YeetTheAnson/AnsonKeyboardNew/assets/render6.png

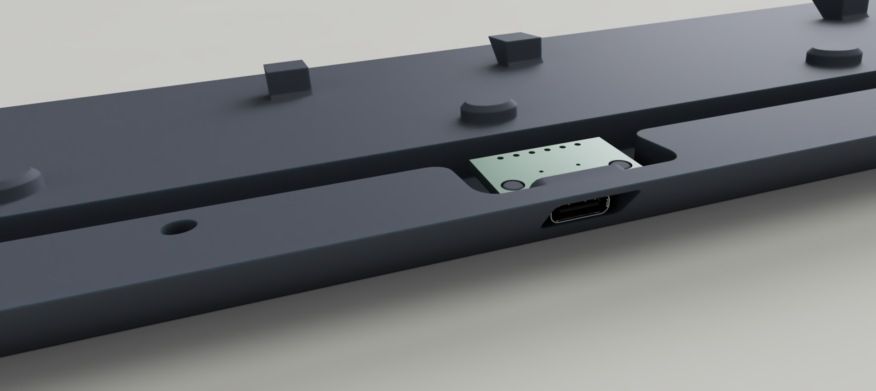
assets/render6.png
