YeetTheAnson/AnsonKeyboardNew/PCB/3d/keycap/DSA_6.25u.step

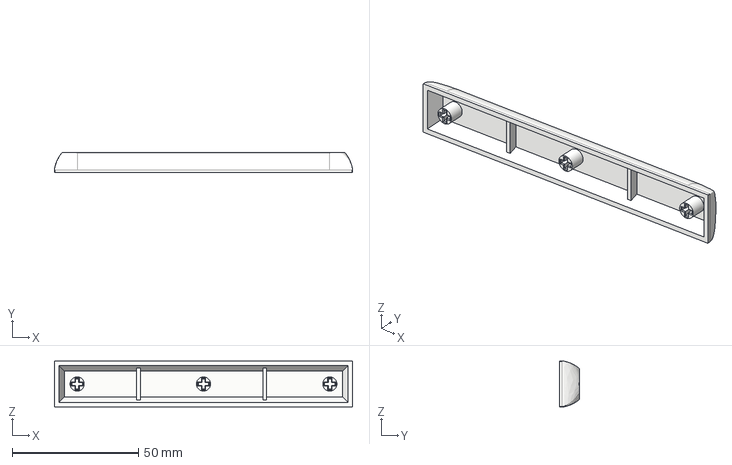
[picture p33: CAD file, 2025-10-06]
PCB/3d/keycap/DSA_6.25u.step
118.0 x 8.00 x 18.2 mm
