YeetTheAnson/AnsonKeyboardNew/PCB/3d/RASPBERRY_PI_PICO.step

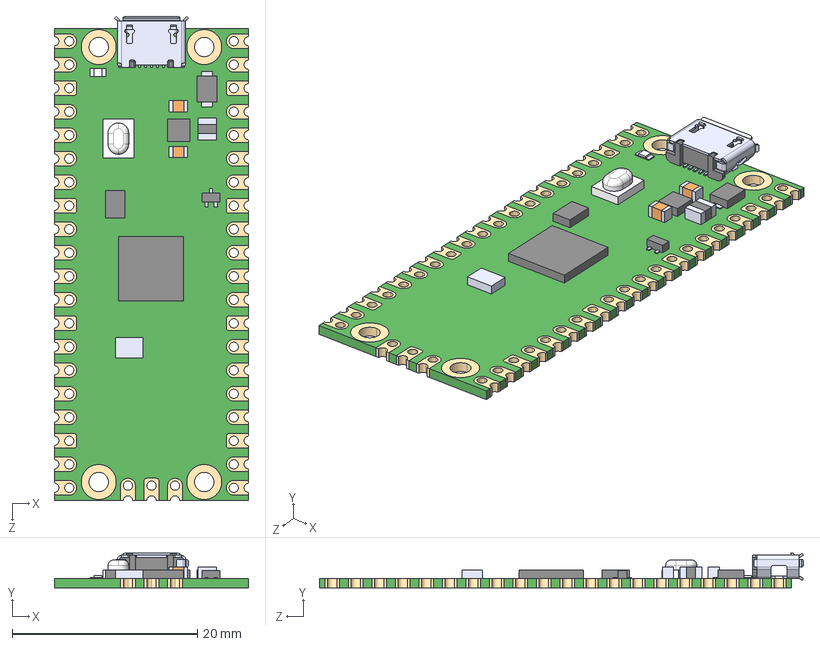
[picture p34: CAD file, 2025-10-06]
PCB/3d/RASPBERRY_PI_PICO.step
21.0 x 3.73 x 52.3 mm
