YeetTheAnson/AnsonKeyboardNew/PCB/3d/keycap/DSA_2u.step

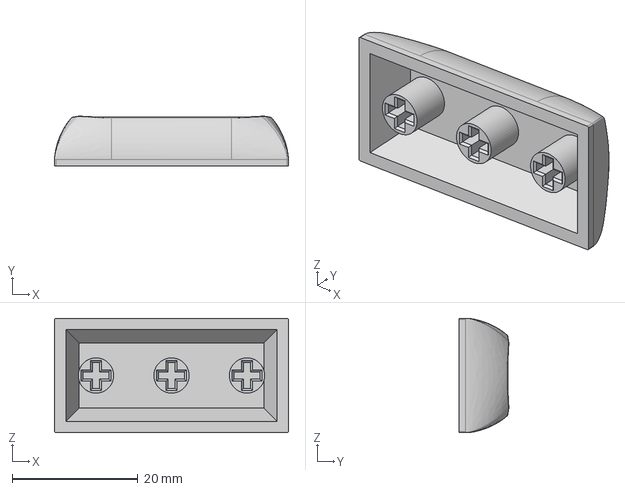
[picture p35: CAD file, 2025-10-06]
PCB/3d/keycap/DSA_2u.step
37.2 x 7.91 x 18.2 mm
