YeetTheAnson/AnsonKeyboardNew/PCB/3d/switch.step

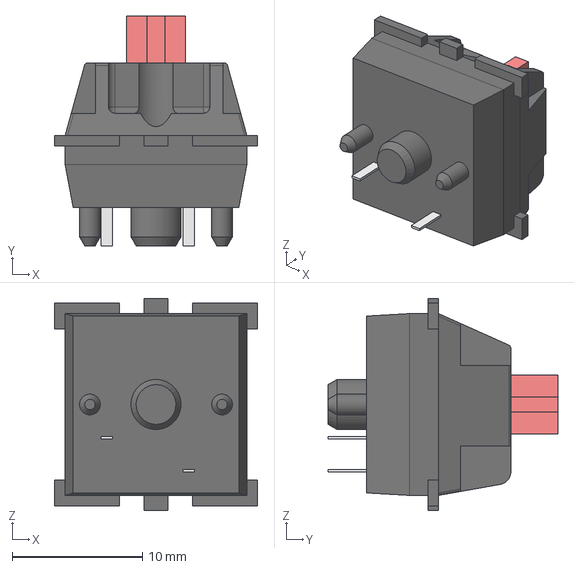
[picture p36: CAD file, 2025-10-06]
PCB/3d/switch.step
15.6 x 17.7 x 16.3 mm
