YeetTheAnson/AnsonKeyboardNew/PCB/3d/keycap/DSA_2.75u.step

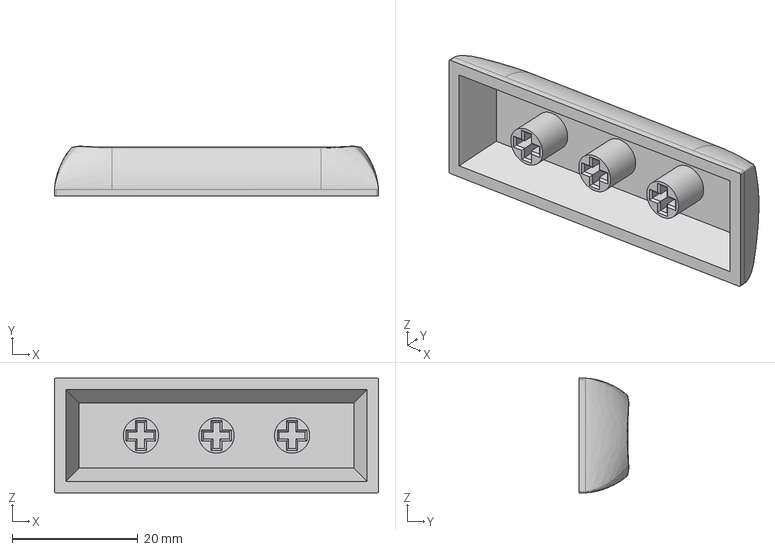
[picture p37: CAD file, 2025-10-06]
PCB/3d/keycap/DSA_2.75u.step
51.5 x 7.91 x 18.2 mm
