YeetTheAnson/AnsonKeyboardNew/PCB/3d/TS-1187A-B-A-B.step

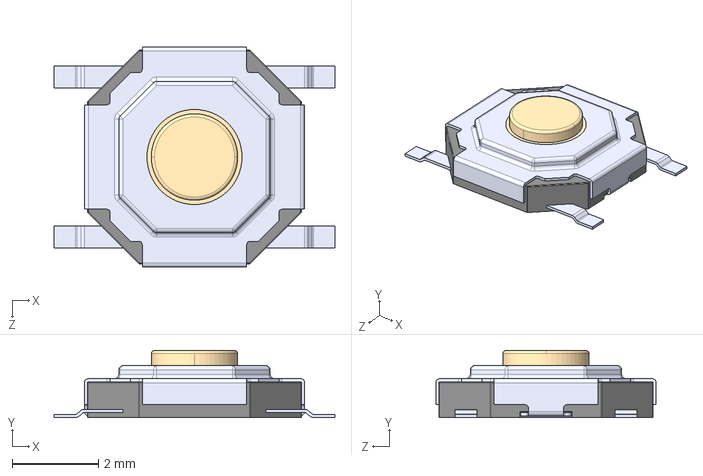
[picture p38: CAD file, 2025-10-06]
PCB/3d/TS-1187A-B-A-B.step
6.50 x 1.55 x 5.10 mm
