YeetTheAnson/AnsonKeyboardNew/PCB/3d/keycap/DSA_1.25u.step

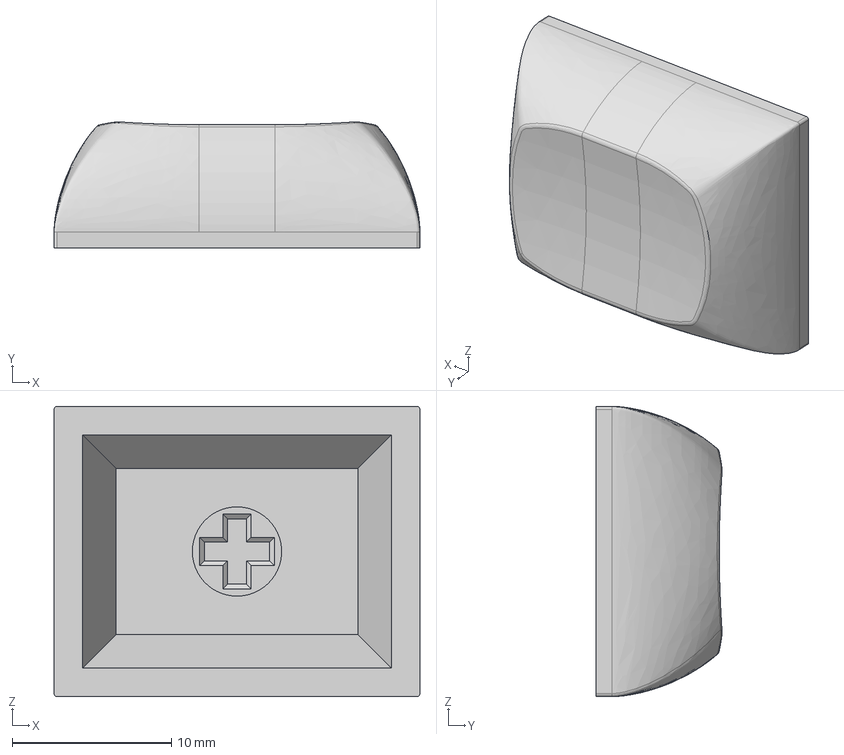
[picture p39: CAD file, 2025-10-06]
PCB/3d/keycap/DSA_1.25u.step
22.9 x 7.91 x 18.2 mm
